profdc9/STM32F4ThruPill/STM32alt-bare.png

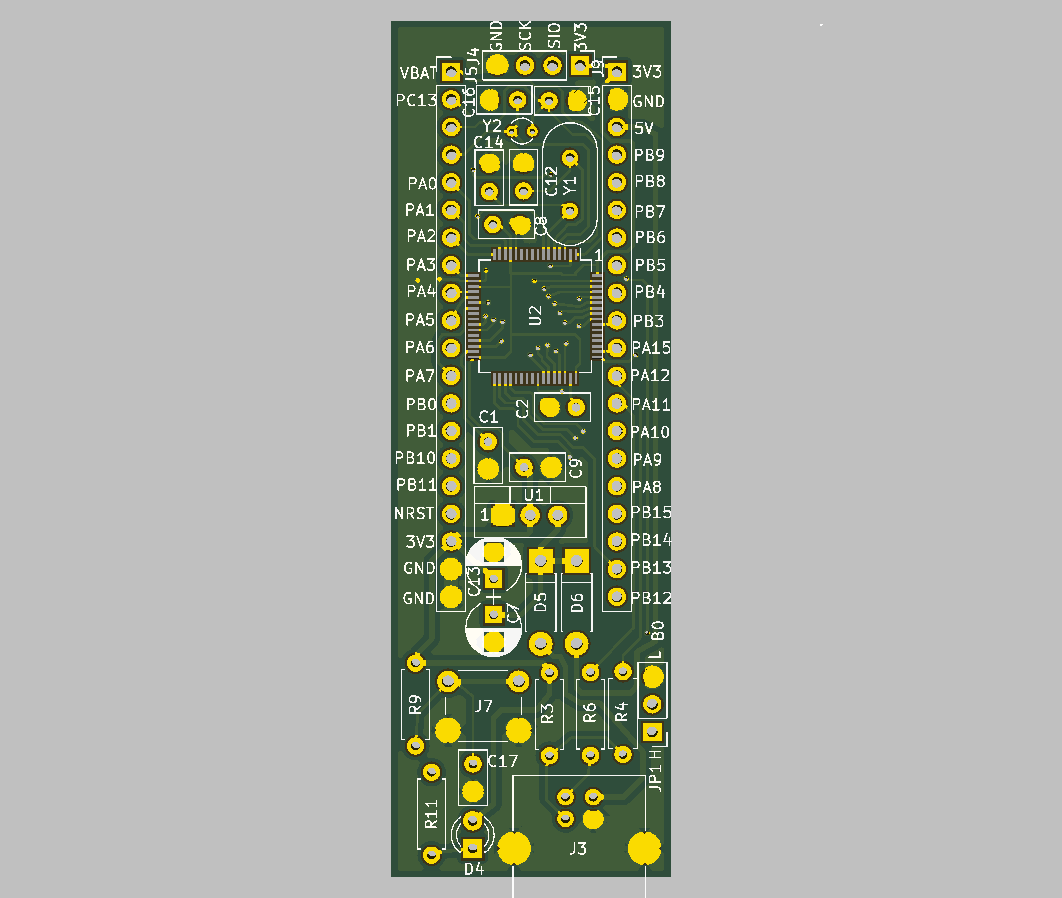
STM32alt-bare.png
